Gaurav12058/UCLA_HAcK_2025/Photos/cad_hat.png

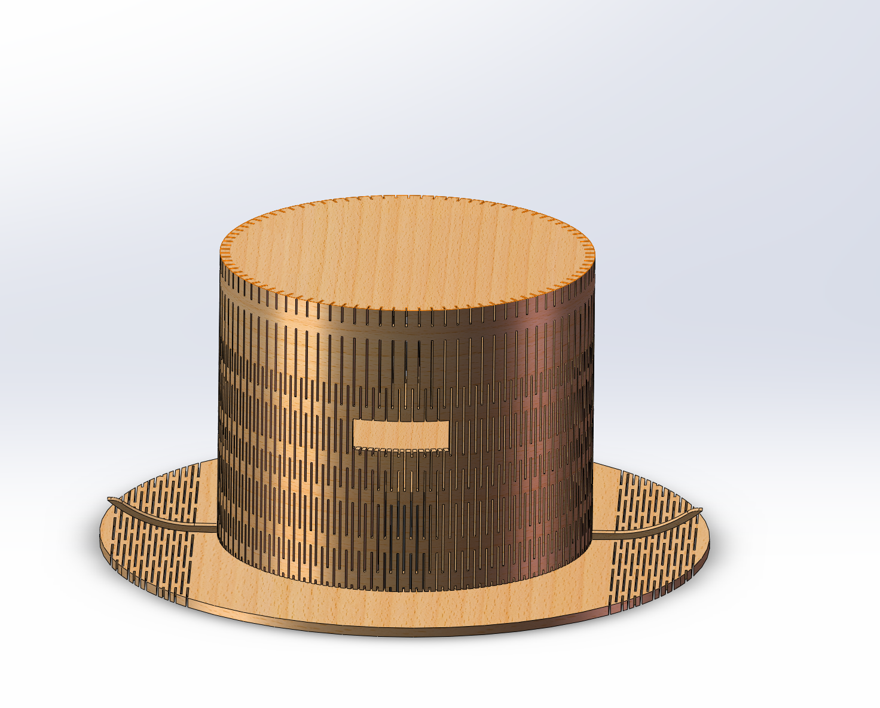
Photos/cad_hat.png
