Gaurav12058/UCLA_HAcK_2025/Photos/circuit_mess.jpg

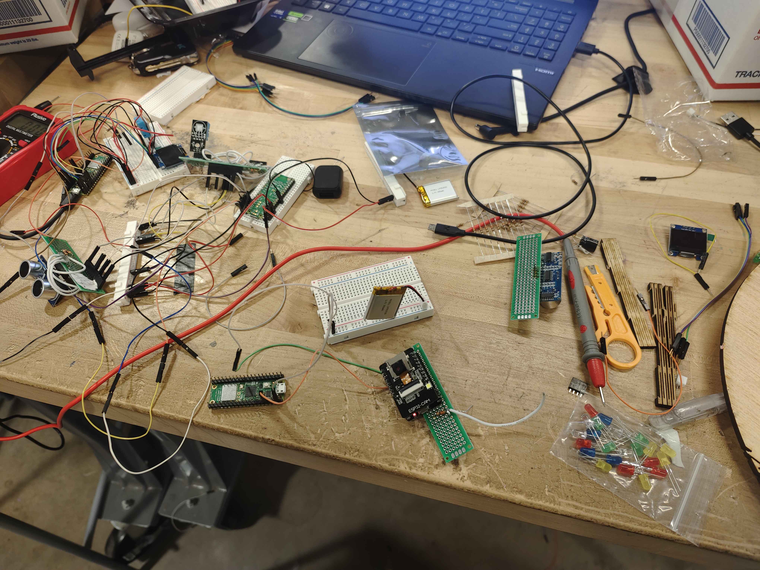
Photos/circuit_mess.jpg
