Gaurav12058/UCLA_HAcK_2025/Photos/cowboy_cad.png

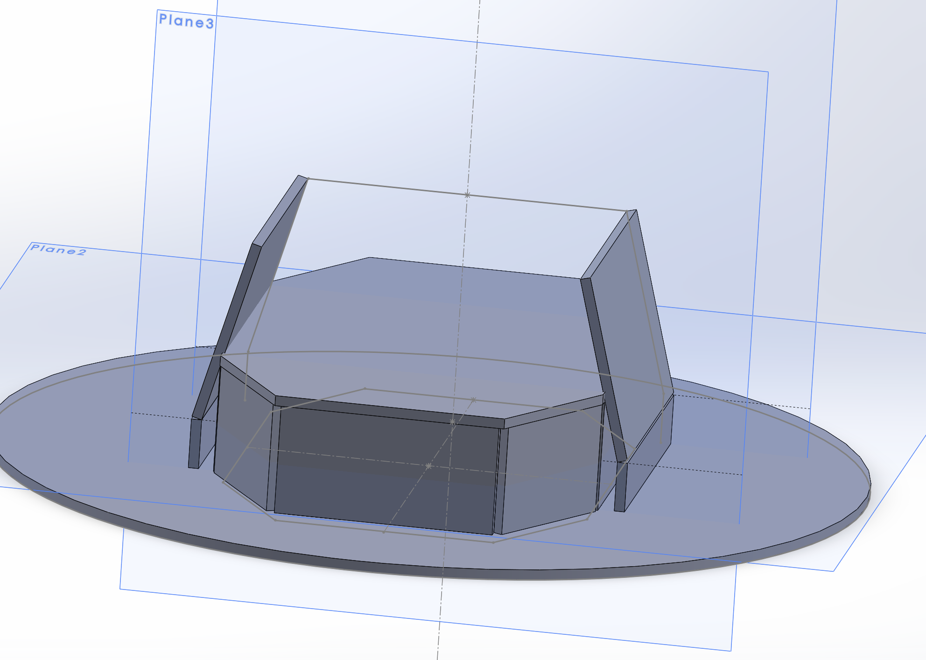
Photos/cowboy_cad.png
