Gaurav12058/UCLA_HAcK_2025/Photos/group_pic.JPG

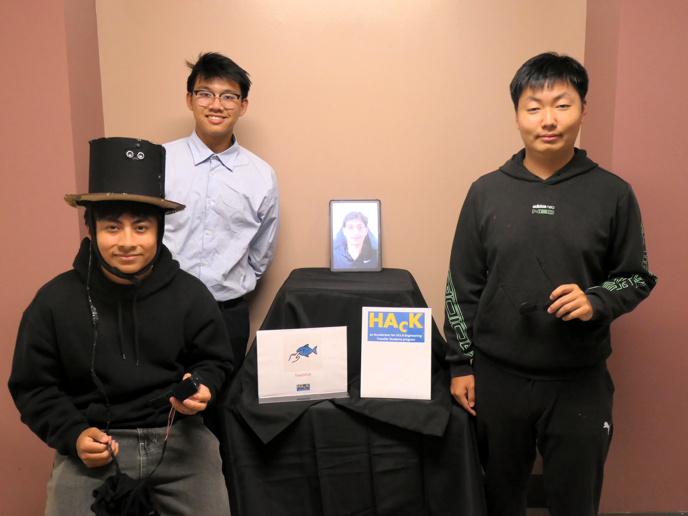
Photos/group_pic.JPG
