Gaurav12058/UCLA_HAcK_2025/Photos/hat_with_circuit_2.jpg

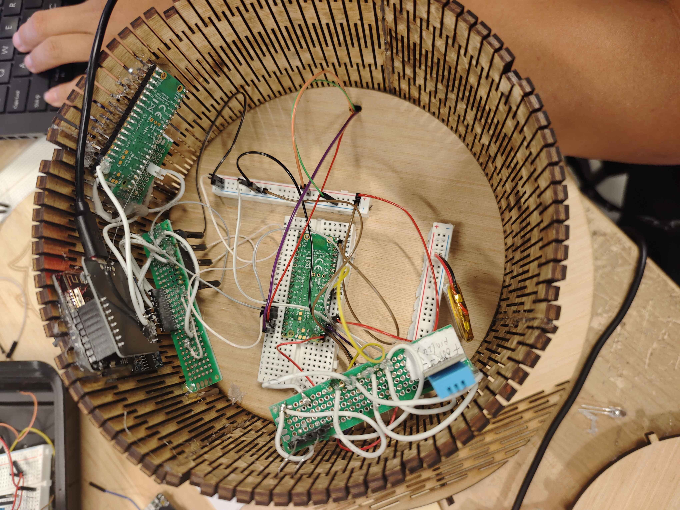
Photos/hat_with_circuit_2.jpg
