Gaurav12058/UCLA_HAcK_2025/Photos/sensor_data_on_website.jpg

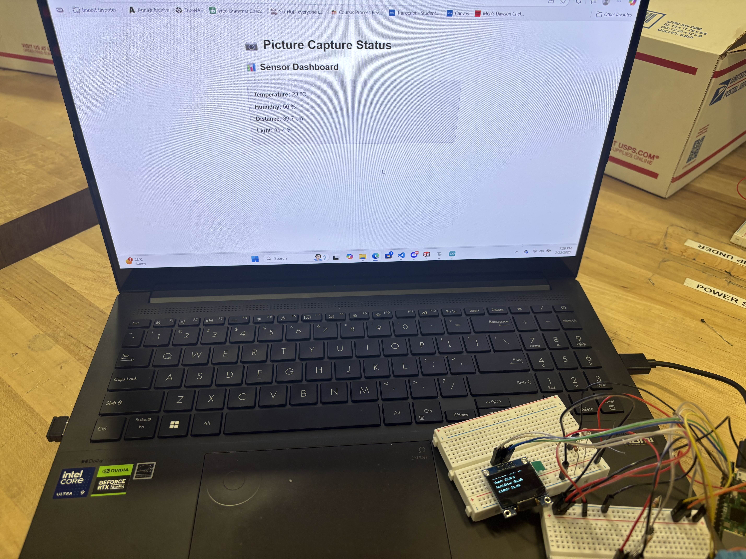
Photos/sensor_data_on_website.jpg
