Gaurav12058/UCLA_HAcK_2025/Photos/website_p1.png

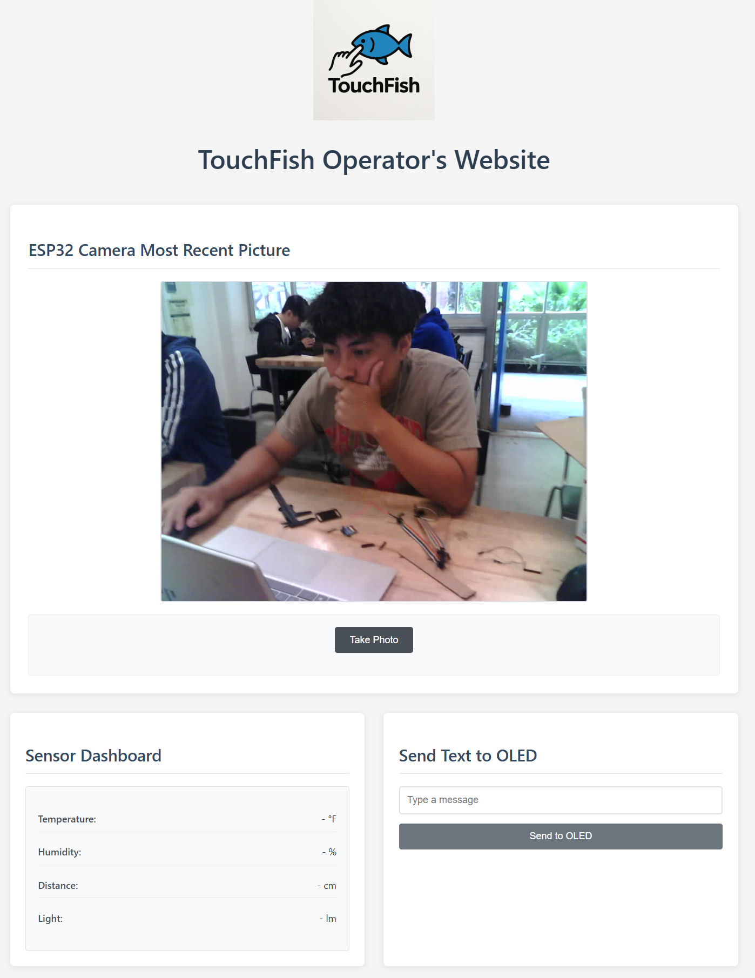
Photos/website_p1.png
