Gaurav12058/UCLA_HAcK_2025/CAD/TopHat/HatCircle.DXF

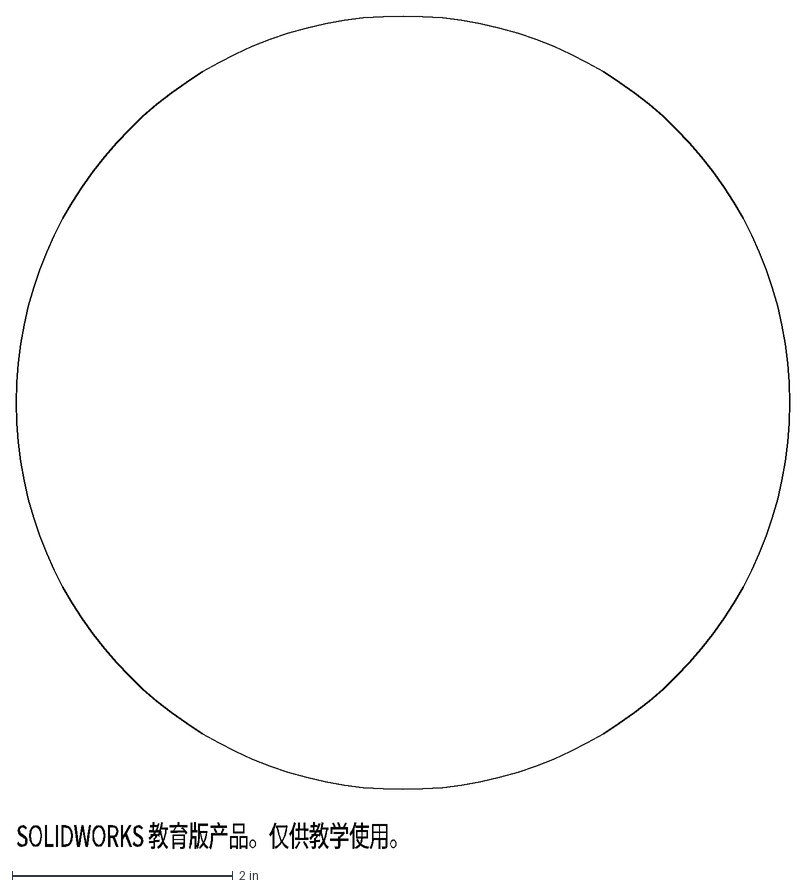
[picture p27: CAD file, 2025-07-29]
CAD/TopHat/HatCircle.DXF
SOLIDWORKS 教育版产品。仅供教学使用。
